SFZ-Soccer/robot-LS/3D-Models/Wien 2026/stl files/Pixy holder.stl

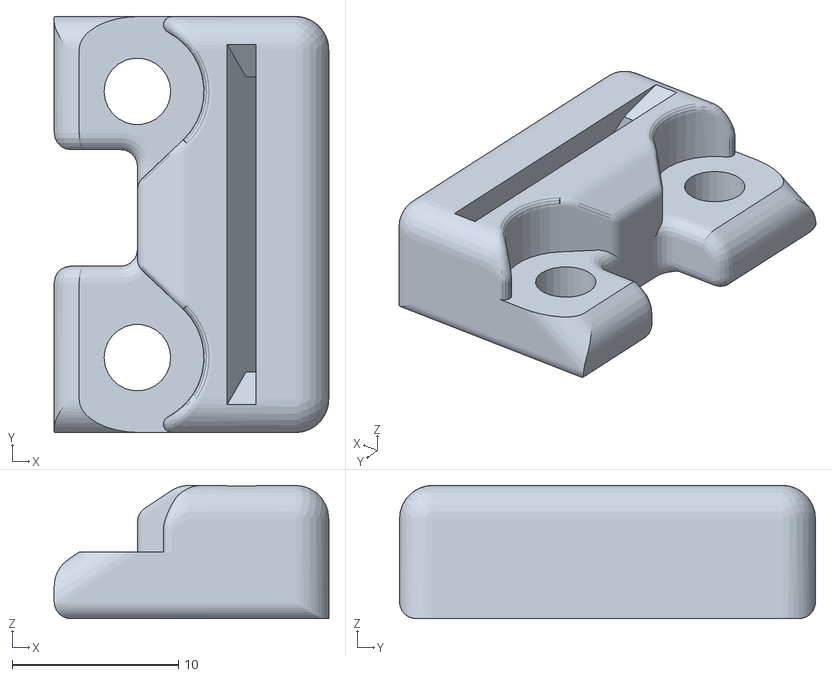
[picture p16: CAD file, 2026-05-31]
3D-Models/Wien 2026/stl files/Pixy holder.stl
16.5 x 25.0 x 8.00
