SFZ-Soccer/robot-LS/3D-Models/Wien 2026/stl files/front iron bar.stl

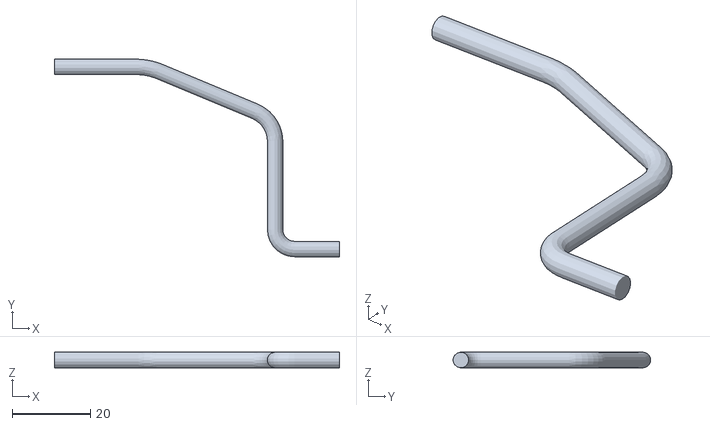
[picture p17: CAD file, 2026-05-31]
3D-Models/Wien 2026/stl files/front iron bar.stl
73.0 x 50.6 x 3.98
