SFZ-Soccer/robot-LS/3D-Models/Wien 2026/stl files/IR-plate.stl

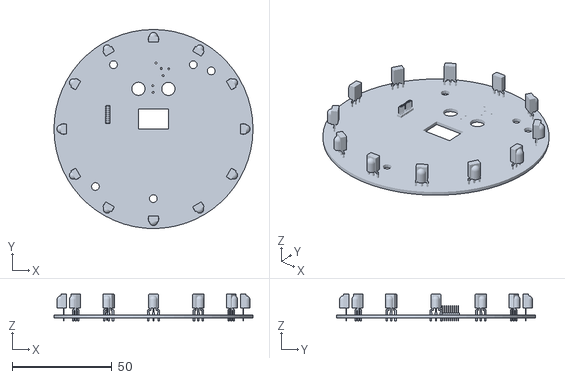
[picture p18: CAD file, 2026-05-31]
3D-Models/Wien 2026/stl files/IR-plate.stl
100.0 x 100.0 x 13.3
