SFZ-Soccer/robot-LS/3D-Models/Wien 2026/stl files/drive and dribbler wheel.stl

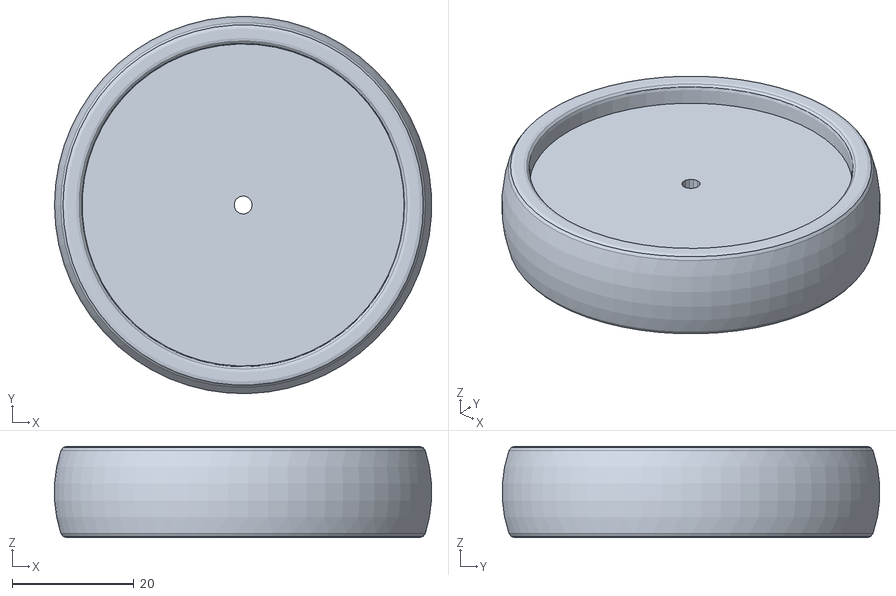
[picture p19: CAD file, 2026-05-31]
3D-Models/Wien 2026/stl files/drive and dribbler wheel.stl
62.0 x 62.1 x 15.0
