SFZ-Soccer/robot-LS/3D-Models/Wien 2026/stl files/Timing belt pulley.stl

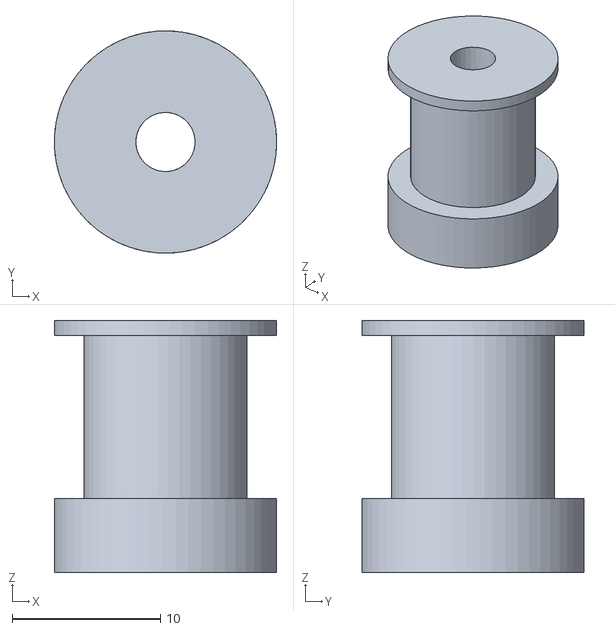
[picture p20: CAD file, 2026-05-31]
3D-Models/Wien 2026/stl files/Timing belt pulley.stl
15.0 x 15.0 x 17.0
