SFZ-Soccer/robot-LS/3D-Models/Wien 2026/stl files/dribbler bar.stl

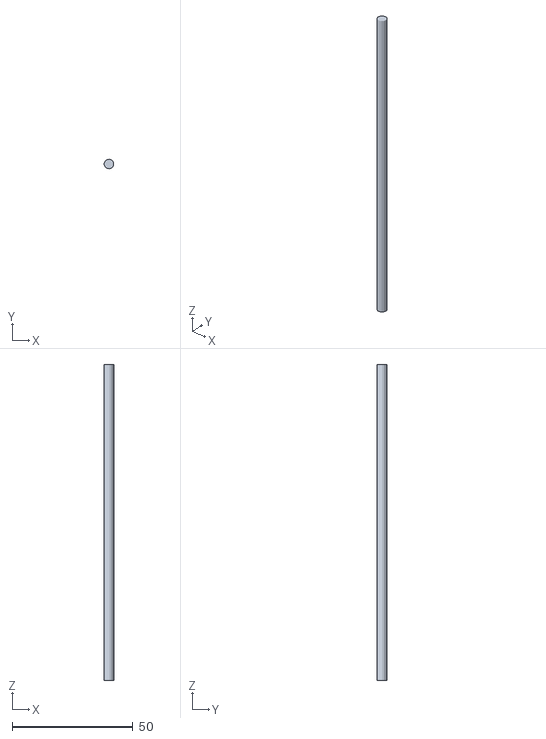
[picture p21: CAD file, 2026-05-31]
3D-Models/Wien 2026/stl files/dribbler bar.stl
3.94 x 3.97 x 131.0
