SFZ-Soccer/robot-LS/3D-Models/Wien 2026/stl files/middle panel.stl

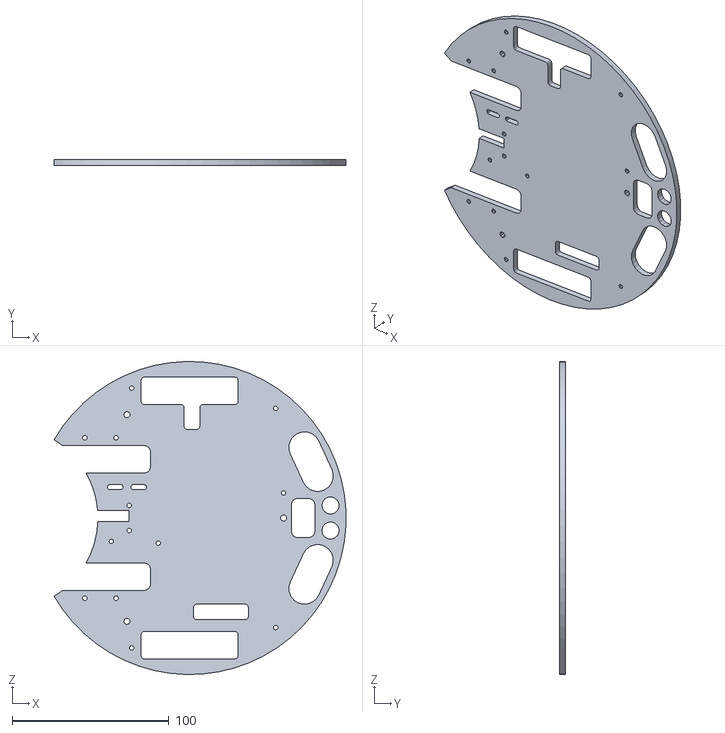
[picture p22: CAD file, 2026-05-31]
3D-Models/Wien 2026/stl files/middle panel.stl
186.5 x 4.00 x 200.0
