SFZ-Soccer/robot-LS/3D-Models/Wien 2026/stl files/motor mount.stl

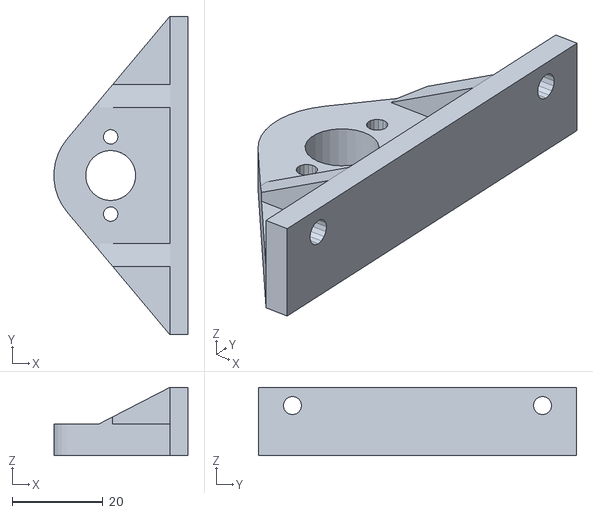
[picture p23: CAD file, 2026-05-31]
3D-Models/Wien 2026/stl files/motor mount.stl
29.5 x 70.0 x 15.0
