SFZ-Soccer/robot-LS/3D-Models/Wien 2026/stl files/Timing belt.stl

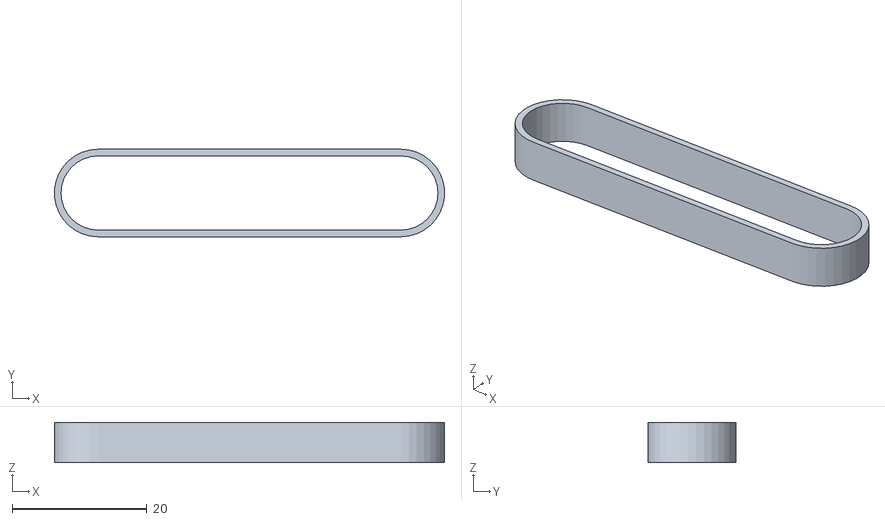
[picture p24: CAD file, 2026-05-31]
3D-Models/Wien 2026/stl files/Timing belt.stl
57.9 x 13.0 x 6.00
