SFZ-Soccer/robot-LS/3D-Models/Wien 2026/stl files/Pixy cam.stl

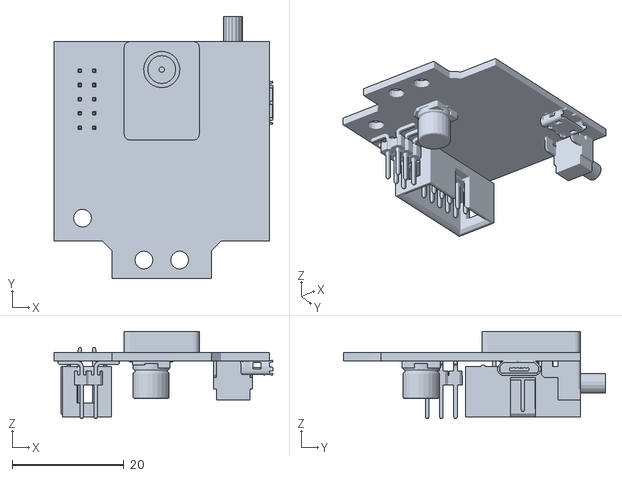
[picture p26: CAD file, 2026-05-31]
3D-Models/Wien 2026/stl files/Pixy cam.stl
39.2 x 46.9 x 15.6
