SFZ-Soccer/robot-LS/3D-Models/Wien 2026/stl files/ball bearing.stl

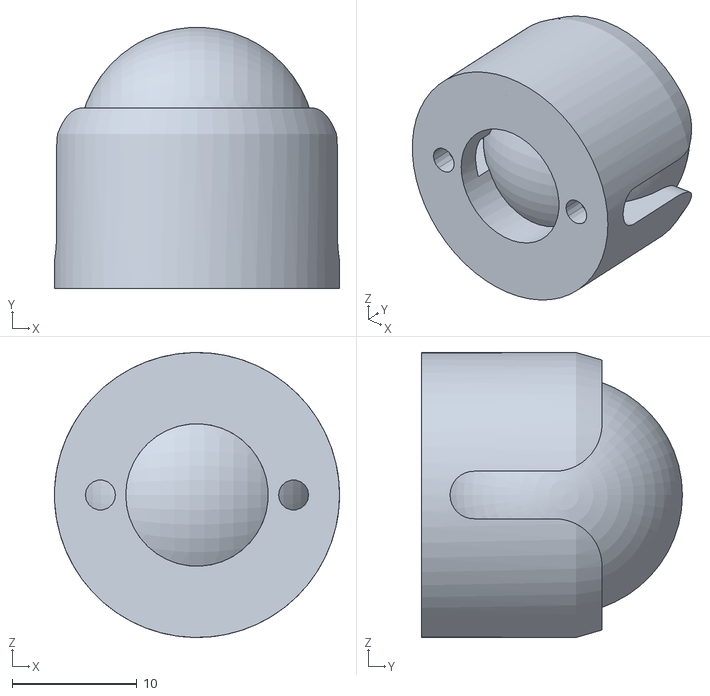
[picture p27: CAD file, 2026-05-31]
3D-Models/Wien 2026/stl files/ball bearing.stl
22.9 x 20.9 x 22.9
