SFZ-Soccer/robot-LS/3D-Models/Wien 2026/stl files/switch.stl

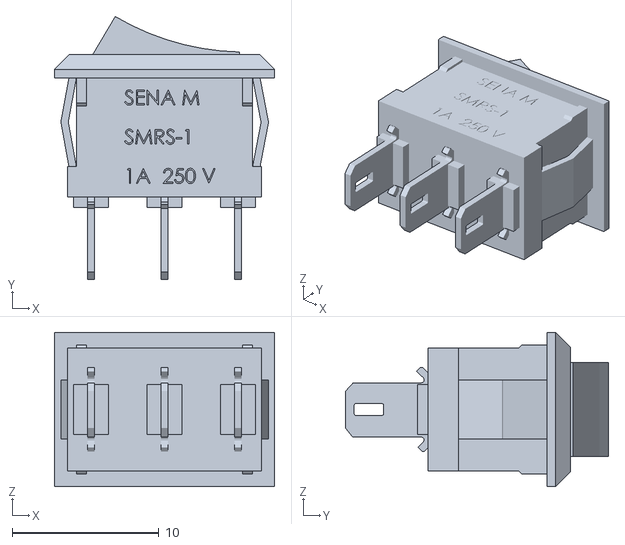
[picture p28: CAD file, 2026-05-31]
3D-Models/Wien 2026/stl files/switch.stl
15.0 x 17.9 x 10.5
