SFZ-Soccer/robot-LS/3D-Models/Wien 2026/stl files/Dribbler motor mount lower section.stl

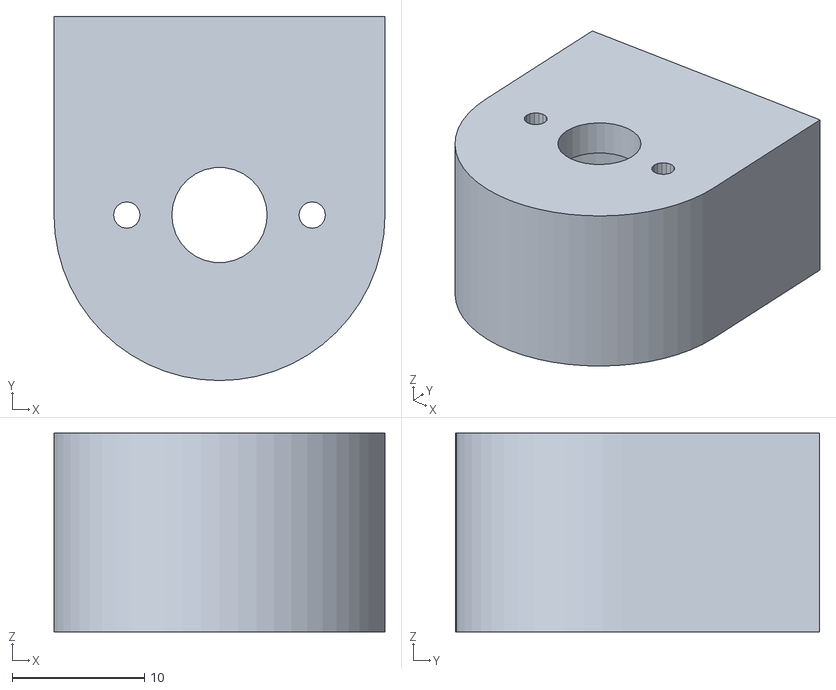
[picture p29: CAD file, 2026-05-31]
3D-Models/Wien 2026/stl files/Dribbler motor mount lower section.stl
25.0 x 27.5 x 15.0
