SFZ-Soccer/robot-LS/Tests/V2/Encoder_Test/Encoder_Test.ino

/**
 * \par Copyright (C), 2012-2016, MakeBlock
 * @file    Me_Auriga_encoder.ino
 * @author  MakeBlock
 * @version V1.0.0
 * @date    2016/07/14
 * @brief   Description: this file is sample code for auriga encoder motor device.
 *
 * Function List:
 *    1. uint8_t MeEncoderOnBoard::getPortB(void);
 *    2. uint8_t MeEncoderOnBoard::getIntNum(void);
 *    3. void MeEncoderOnBoard::pulsePosPlus(void);
 *    4. void MeEncoderOnBoard::pulsePosMinus(void);
 *    5. void MeEncoderOnBoard::setMotorPwm(int pwm);
 *    6. double MeEncoderOnBoard::getCurrentSpeed(void);
 *    7. void MeEncoderOnBoard::setSpeedPid(float p,float i,float d);
 *    8. void MeEncoderOnBoard::setPosPid(float p,float i,float d);
 *    7. void MeEncoderOnBoard::setPosPid(float p,float i,float d);
 *    8. void MeEncoderOnBoard::setPulse(int16_t pulseValue);
 *    9. void MeEncoderOnBoard::setRatio(int16_t RatioValue);
 *    10. void MeEncoderOnBoard::runSpeed(float speed);
 *    11. void MeEncoderOnBoard::loop(void);
 *
 * \par History:
 * <pre>
 * <Author>     <Time>        <Version>      <Descr>
 * Mark Yan     2016/07/14    1.0.0          build the new
 * </pre>
 */

#include <MeAuriga.h>

MeEncoderOnBoard Encoder_1(SLOT1);
MeEncoderOnBoard Encoder_2(SLOT2);

void isr_process_encoder1(void)
{
  if(digitalRead(Encoder_1.getPortB()) == 0)
  {
    Encoder_1.pulsePosMinus();
  }
  else
  {
    Encoder_1.pulsePosPlus();;
  }
}

void isr_process_encoder2(void)
{
  if(digitalRead(Encoder_2.getPortB()) == 0)
  {
    Encoder_2.pulsePosMinus();
  }
  else
  {
    Encoder_2.pulsePosPlus();
  }
}

void setup()
{
  attachInterrupt(Encoder_1.getIntNum(), isr_process_encoder1, RISING);
  attachInterrupt(Encoder_2.getIntNum(), isr_process_encoder2, RISING);
  Serial.begin(9600);
}

void loop()
{
  Encoder_1.loop();
  Encoder_2.loop();
  Serial.print("Spped 1:");
  Serial.print(Encoder_1.getCurrentSpeed());
  Serial.print(" ,Spped 2:");
  Serial.println(Encoder_2.getCurrentSpeed());
}
